simonjgreen/BinRange/hardware/wrover-case/makerworld/wrover-case-din-rail/Pasted image.png

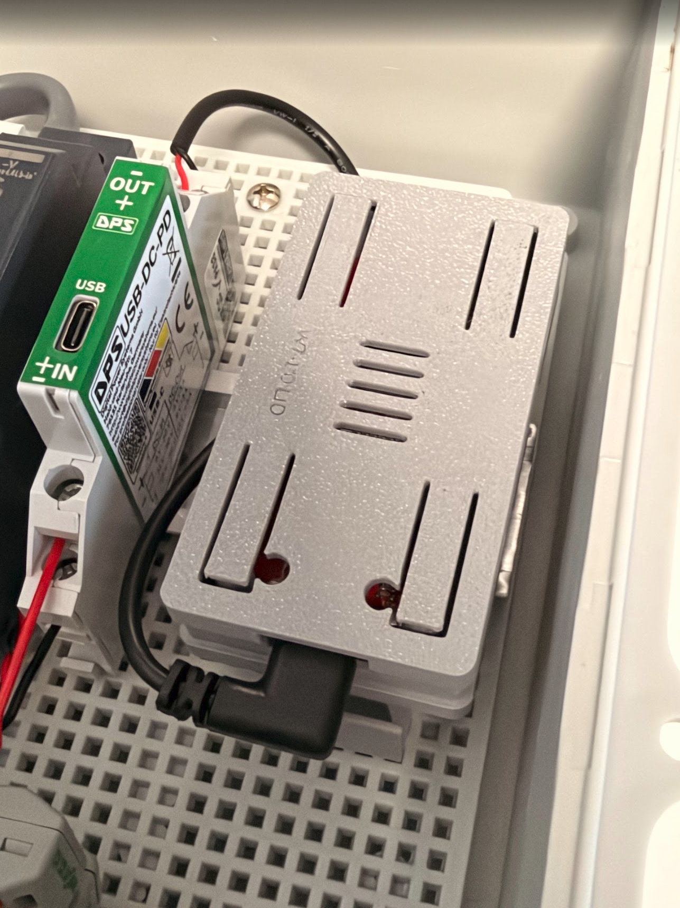
hardware/wrover-case/makerworld/wrover-case-din-rail/Pasted image.png
