simonjgreen/BinRange/hardware/wrover-case/makerworld/wrover-case-din-rail/wrover-case-v7.2.0-exploded.png

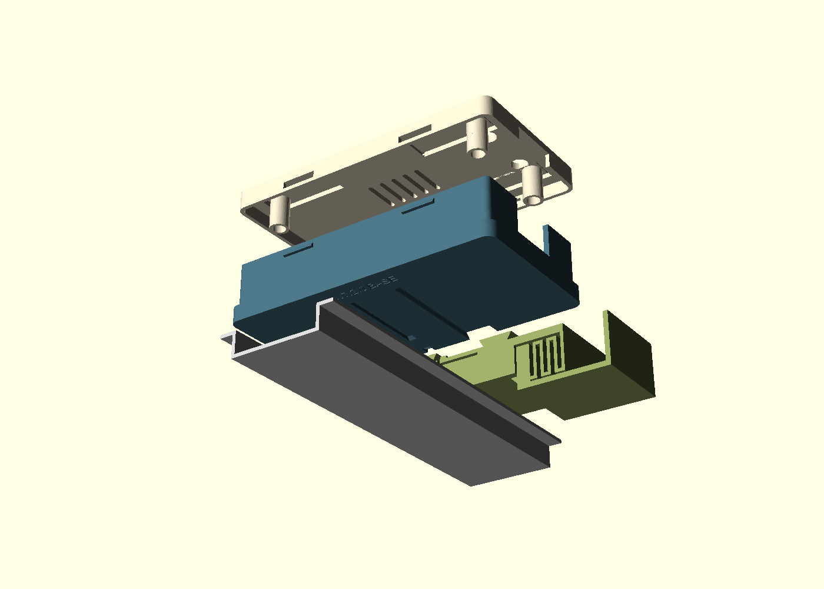
hardware/wrover-case/makerworld/wrover-case-din-rail/wrover-case-v7.2.0-exploded.png
