simonjgreen/BinRange/hardware/wrover-case/makerworld/wrover-case-standalone/Pasted image (3).png

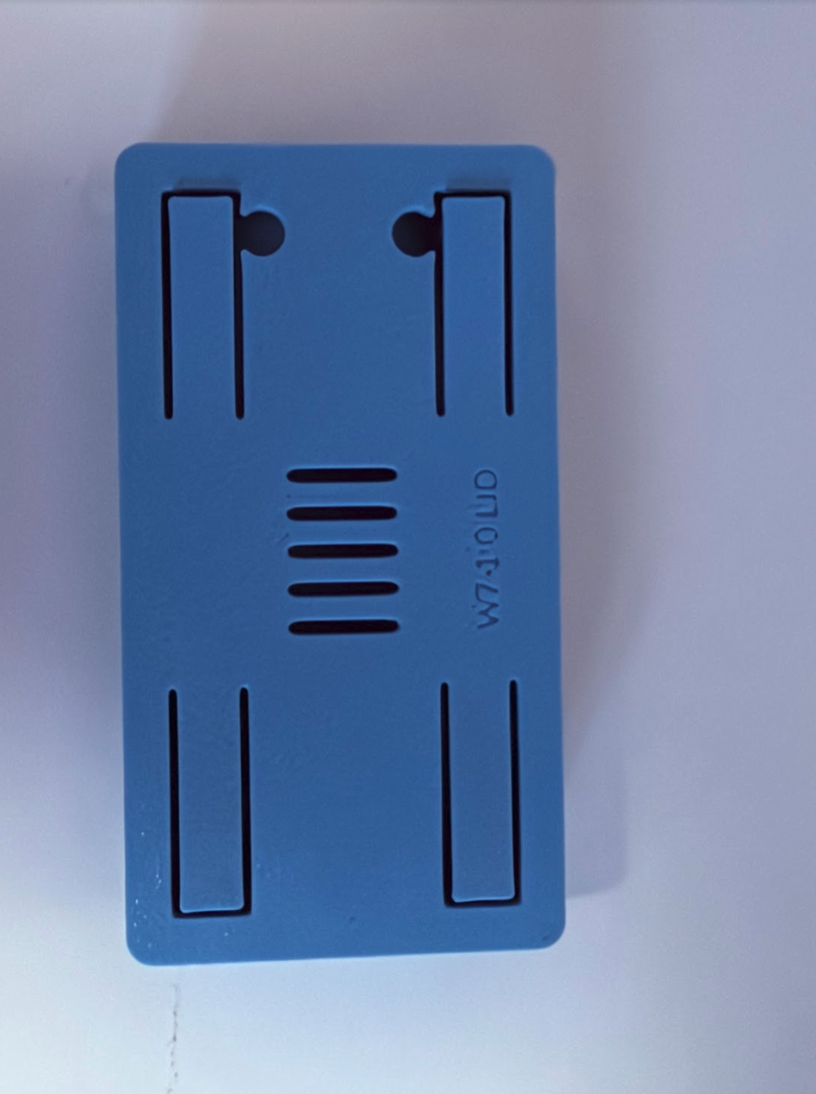
hardware/wrover-case/makerworld/wrover-case-standalone/Pasted image (3).png
