simonjgreen/BinRange/hardware/wrover-case/makerworld/wrover-case-standalone/Pasted image.png

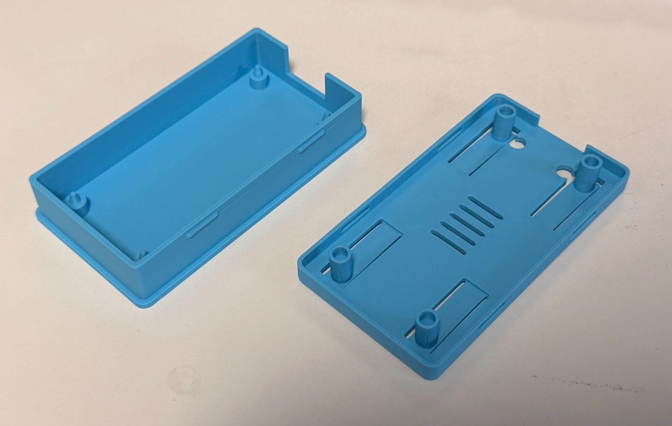
hardware/wrover-case/makerworld/wrover-case-standalone/Pasted image.png
