simonjgreen/BinRange/hardware/wrover-case/makerworld/wrover-case-standalone/wrover-case-v7.1.0-exploded.png

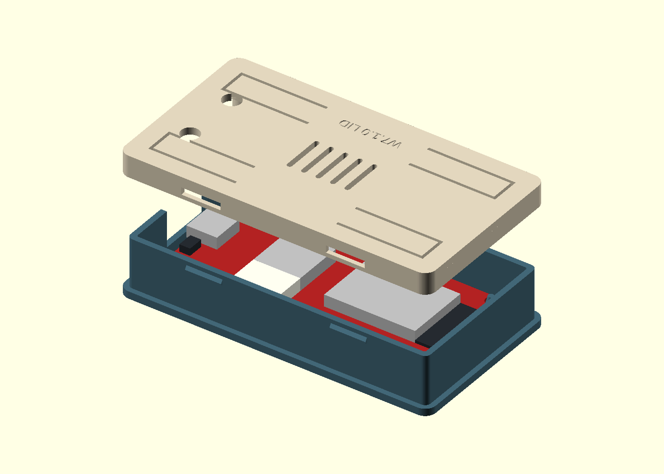
hardware/wrover-case/makerworld/wrover-case-standalone/wrover-case-v7.1.0-exploded.png
